Anderman/tombask/src/webui/controlApi.h

#pragma once

#include <ArduinoJson.h>

void handleGetStatus();
void handlePostSetpoint();
void handlePostFan();
void handlePostBoost();
void handlePostLegionellaOn();
void handlePostLegionellaHour();
void handlePostLegionellaTemp();
