Anderman/tombask/src/rs485/sensors.cpp

#include "sensors.h"
#include <Arduino.h>
#include <globals.h> // mqttClient
#include "storage/storage.h"
#include "settings.h"
#include "../mqtt/mqtt_properties.h"
#include "../mqtt/discovery.h"
#include "../mqtt/state.h"
