Anderman/tombask/src/rs485/rs485.cpp

#include <HardwareSerial.h>
#include "globals.h"
#include "rs485.h"
#include "rs485_1c.h"
#include "rs485_2d.h"
#include "rs485_25_5.h"
#include "rs485_25_6.h"
#include "rs485_40.h"
#include "rs485_3c.h"
#include <webui/webLogger.h>
#include "sensors.h"
#include "settings.h"

static HardwareSerial RS485(1);
static constexpr uint32_t RS485_RESPONSE_DELAY_US = 7000;
static uint8_t buffer[0x48];
static int bufferPos = 0;
static uint8_t length = 8;

static bool verifyCrc(const uint8_t *data, size_t len);
static void frameReader();
static bool formatFrameLine(const uint8_t *data, size_t len, char *out, size_t outSize);
static uint16_t crc16_modbus(const uint8_t *data, size_t len);
static bool write_1c_next = false;

void setupRs485()
{
    buffer[0] = 0x7e;
    buffer[1] = 0x7e;

    pinMode(DE_RE_PIN, OUTPUT);
    digitalWrite(DE_RE_PIN, LOW);
    RS485.begin(9600, SERIAL_8N1, RX_PIN, TX_PIN);
    Serial.printf("[rs485] begin 9600 8N1 rx=IO%u tx=IO%u de_re=IO%u (uart1 half-duplex)\n",
                  (unsigned)RX_PIN,
                  (unsigned)TX_PIN,
                  (unsigned)DE_RE_PIN);
}

void rs485Loop()
{
    while (RS485.available())
    {
        uint8_t c = RS485.read();
        if (bufferPos == 0 && c == 0x7E)
        {
            bufferPos++;
        }
        else if (bufferPos == 1 && c == 0x7E)
        {
            bufferPos++;
        }
        else if (bufferPos > 1 && bufferPos < length)
        {
            if (bufferPos == 5)
            {
                length = 5 + c + 3;
            }
            buffer[bufferPos++] = c;
            if (bufferPos == length)
            {
                char line[3 * 0x48 + 32];
                const bool crcOk = formatFrameLine(buffer, length, line, sizeof(line));
                Serial.println(line);
                webLoggerWriteLine(line);
                if (crcOk)
                {
                    if (buffer[2] == 0xf0 && buffer[3] == 0xf0)
                    {
                        frameReader();
                    }
                    if (ControlValueChanged && buffer[2] == 0x02 && buffer[3] == 0xf0 && buffer[5] == 0x04)
                    {
                        delayMicroseconds(RS485_RESPONSE_DELAY_US);
                        if (!write_1c_next)
                        {
                            const uint8_t len = get_2dFrame(buffer);
                            WriteFrame(len, false);
                        }
                        else
                        {
                            const uint8_t len = get_1cFrame(buffer);
                            WriteFrame(len, true);
                            ControlValueChanged = false;
                        }
                    }
                }
                bufferPos = 0;
                length = 8;
            }
        }
    }
}

void WriteFrame(const uint8_t len, const bool isLast)
{
    const uint16_t crc = crc16_modbus(buffer, len - 3);
    buffer[len - 3] = crc & 0xFF;           // lage byte
    buffer[len - 2] = (crc >> 8) & 0xFF;    // hoge byte
    buffer[len - 1] = isLast ? 0x55 : 0x00; // stopbyte
    digitalWrite(DE_RE_PIN, HIGH);
    delayMicroseconds(100);
    RS485.write(buffer, len);
    RS485.flush();
    delayMicroseconds(100);
    digitalWrite(DE_RE_PIN, LOW);
    char txLine[3 * 0x48 + 32];
    formatFrameLine(buffer, len, txLine, sizeof(txLine));
    webLoggerWriteLine(txLine);
    write_1c_next = !isLast;
}

static uint16_t crc16_modbus(const uint8_t *data, size_t len)
{
    uint16_t crc = 0xFFFF;
    for (size_t i = 0; i < len; i++)
    {
        crc ^= data[i];
        for (int j = 0; j < 8; j++)
        {
            if (crc & 1)
                crc = (crc >> 1) ^ 0xA001;
            else
                crc >>= 1;
        }
    }
    return crc;
}

static bool verifyCrc(const uint8_t *data, size_t len)
{
    if (len < 3)
        return false; // Minimaal 1 byte data + 2 bytes CRC
    uint16_t receivedCrc = data[len - 3] | (data[len - 2] << 8);
    uint16_t calculatedCrc = crc16_modbus(data, len - 3);
    if (receivedCrc != calculatedCrc)
    {
        Serial.printf("CRC mismatch: received 0x%04X, calculated 0x%04X\n", receivedCrc, calculatedCrc);
    }
    return receivedCrc == calculatedCrc;
}

static void frameReader()
{
    const uint8_t length = buffer[5];
    const uint8_t func = buffer[8];
    switch (length)
    {
    case 0x1c:
        return read_1c(buffer);
    case 0x25:
        return func == 5 ? read_25_5(buffer) : read_25_6(buffer);
    case 0x2d:
        return read_2d(buffer);
    case 0x3c:
        return read_3c(buffer);
    case 0x40:
        return read_40(buffer);
    }
    Serial.println(String("Unknown frame length: ") + String(length, HEX));
}
static bool formatFrameLine(const uint8_t *data, size_t len, char *out, size_t outSize)
{
    if (!out || outSize == 0)
        return false;

    size_t pos = 0;

    for (size_t i = 0; i < len && pos + 3 < outSize; i++)
        pos += snprintf(out + pos, outSize - pos, "%02X ", data[i]);

    if (pos > 0 && out[pos - 1] == ' ')
        out[pos - 1] = '\0'; // laatste spatie weg
    else if (pos == 0)
        out[0] = '\0';

    const bool crcOk = verifyCrc(data, len);

    const size_t used = strlen(out);
    if (used < outSize)
        snprintf(out + used, outSize - used, " | CRC %s", crcOk ? "OK" : "ERROR");

    return crcOk;
}
