Anderman/tombask/src/status_led.cpp

#include "status_led.h"
#include <Adafruit_NeoPixel.h>
#include "globals.h"

static Adafruit_NeoPixel g_strip(1, STATUS_LED_PIN, NEO_GRB + NEO_KHZ800);

void statusLedSetup()
{
    g_strip.begin();
    g_strip.setBrightness(32);
    g_strip.show();
}

void statusLedSetRgb(uint8_t r, uint8_t g, uint8_t b)
{
    g_strip.setPixelColor(0, g_strip.Color(r, g, b));
    g_strip.show();
}
