Anderman/tombask/src/rs485/settings.h

#pragma once
#include <stdint.h>


struct ControlValues
{
    uint8_t SetpointTemp;
    uint8_t LegionellaTemp;
    uint8_t TopTemp;
    uint8_t BottomTemp;
    uint8_t LegionellaHour;
    uint16_t Power ;
    bool Heating;
    bool Fan;
    bool Boost;
    bool LegionellaOn;
};
extern bool ControlValueChanged;
extern ControlValues controlValues;
